git4dcc/RTB_D99/supplemental/images/D99_usecase3.jpg

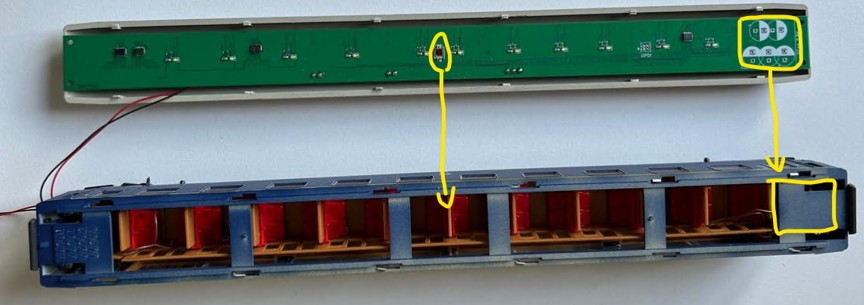
supplemental/images/D99_usecase3.jpg
